SilkT/function-generator/Inc/octaves.h

#define oct_1 16
#define oct_2 32
#define oct_3 63
#define oct_4 125
#define oct_5 250
#define oct_6 500
#define oct_7 1000
#define oct_8 2000
#define oct_9 4000
#define oct_10 8000
#define oct_11 16000



switch (F)
{
    case /* constant-expression */:
        /* code */
        break;

    default:
        break;
}
